joshnishikawa/MomiPlug/src/midi/ChaosEngine.cpp

#include "ChaosEngine.h"

ChaosEngine chaosEngine;

ChaosEngine::ChaosEngine()
    : inLo(TouchConfig::CHAOS_IN_LO),
      inHi(TouchConfig::CHAOS_IN_HI),
      lastRawTouch(0),
      activeNote(0),
      waiting(false),
      waitTimeMs(0),
      noteTimer(0),
      pollTimer(0) {}

void ChaosEngine::calibrateBaseline() {
    // No dynamic calibration loop on boot - use fixed, stable thresholds
    inLo = TouchConfig::CHAOS_IN_LO;
    inHi = TouchConfig::CHAOS_IN_HI;
    lastRawTouch = 0;
}

void ChaosEngine::silence(uint8_t midiChannel) {
    if (activeNote > 0) {
        usbMIDI.sendNoteOn(activeNote, 0, midiChannel);
        activeNote = 0;
    }
    waiting = false;
}

void ChaosEngine::update(uint8_t midiChannel, const bool dinChords[12], const bool usbChords[12]) {
    if (pollTimer < TouchConfig::CHAOS_POLL_MS) {
        return;
    }
    pollTimer = 0;

    int rawTouch = touchRead(Pins::TOUCH_CHAOS_PAD);
    lastRawTouch = rawTouch;

    // In ECHO mode (or NONE), do not play CAOS synth notes
    uint8_t expMode = configMgr.getExpMode();
    if (expMode != EXP_CAOS && expMode != EXP_BOTH) {
        if (activeNote > 0) {
            silence(midiChannel);
        }
        return;
    }

    // Below touch threshold: silence note
    if (rawTouch < inLo) {
        silence(midiChannel);
        return;
    }

    uint16_t mappedNote = map(
        rawTouch,
        inLo,
        inHi,
        TouchConfig::CHAOS_NOTE_MIN,
        TouchConfig::CHAOS_NOTE_MAX
    );
    mappedNote = constrain(mappedNote, TouchConfig::CHAOS_NOTE_MIN, TouchConfig::CHAOS_NOTE_MAX);

    if (waiting) {
        if (noteTimer > waitTimeMs) {
            waiting = false;
        }
    }
    else if (mappedNote > 0) {
        uint8_t pitchClass = mappedNote % 12;
        // Trigger note only if pitch class is present in active DIN or USB chords
        if ((dinChords[pitchClass] || usbChords[pitchClass]) && mappedNote != activeNote) {
            if (activeNote > 0) {
                usbMIDI.sendNoteOn(activeNote, 0, midiChannel); // Silence previous note
            }
            usbMIDI.sendNoteOn(mappedNote, TouchConfig::CHAOS_VELOCITY, midiChannel);
            waitTimeMs = (mappedNote < 150) ? (150 - mappedNote) : 10;
            activeNote = static_cast<uint8_t>(mappedNote);
            noteTimer = 0;
            waiting = true;
        }
    }
}
