joshnishikawa/MomiPlug/MOMI3/editor.h

#ifndef editor_h
#define editor_h

#include "Arduino.h"
#include "SevSeg.h"
#include "MIDIcontroller.h"
extern byte MIDIchannel;
extern SevSeg DSP;

class Editor{
    int quadOne(byte val, byte max);
    char DSPstring[5];
    byte DP;
  public:
    Editor();
    Editor(int a, int b, int p);
    ~Editor();
    Bounce* bounce;
    Encoder* encoder;
    int number;
    int level;
    uint8_t editing;
    int target;
    int newInLo, newInHi;
    byte editChannel();
    uint8_t setAnalog(int p);
    int send(); //cuz interrupts won't let two objects use the same encoder pins
};
#endif
